jrperin/homeControl_esp8266/exemplos/server/server.ino

/*
The MIT License (MIT)
Copyright (c) 2015 Pedro Minatel
Permission is hereby granted, free of charge, to any person obtaining a copy
of this software and associated documentation files (the "Software"), to deal
in the Software without restriction, including without limitation the rights
to use, copy, modify, merge, publish, distribute, sublicense, and/or sell
copies of the Software, and to permit persons to whom the Software is
furnished to do so, subject to the following conditions:
The above copyright notice and this permission notice shall be included in all
copies or substantial portions of the Software.
THE SOFTWARE IS PROVIDED "AS IS", WITHOUT WARRANTY OF ANY KIND, EXPRESS OR
IMPLIED, INCLUDING BUT NOT LIMITED TO THE WARRANTIES OF MERCHANTABILITY,
FITNESS FOR A PARTICULAR PURPOSE AND NONINFRINGEMENT. IN NO EVENT SHALL THE
AUTHORS OR COPYRIGHT HOLDERS BE LIABLE FOR ANY CLAIM, DAMAGES OR OTHER
LIABILITY, WHETHER IN AN ACTION OF CONTRACT, TORT OR OTHERWISE, ARISING FROM,
OUT OF OR IN CONNECTION WITH THE SOFTWARE OR THE USE OR OTHER DEALINGS IN THE
SOFTWARE.
*/

#include <ESP8266WiFi.h>

const char* ssid = "ssid";
const char* password = "password";

WiFiServer server(80);

void setup() {
  Serial.begin(115200);
  delay(10);

  // prepare GPIO2
  pinMode(4, OUTPUT);
  digitalWrite(4, 0);

  pinMode(5, OUTPUT);
  digitalWrite(5, 0);
  
  // Connect to WiFi network
  Serial.println();
  Serial.println();
  Serial.print("Connecting to ");
  Serial.println(ssid);
  
  WiFi.begin(ssid, password);
  
  while (WiFi.status() != WL_CONNECTED) {
    delay(500);
    Serial.print(".");
  }
  
  Serial.println("");
  Serial.println("WiFi connected");
  
  // Start the server
  server.begin();
  Serial.println("Server started");
  Serial.println(WiFi.localIP());
}

void loop() {
  WiFiClient client = server.available();
  if (!client) {
    return;
  }
  
  Serial.println("new client");
  while(!client.available()){
    delay(1);
  }
  
  String req = client.readStringUntil('\r');
  Serial.println(req);
  client.flush();

  String buf = "";

  buf += "HTTP/1.1 200 OK\r\nContent-Type: text/html\r\n\r\n<!DOCTYPE HTML>\r\n<html>\r\n";
  buf += "<h3> ESP8266 Web Server</h3>";
  buf += "<p>GPIO4 <a href=\"?function=led4_on\"><button>ON</button></a> <a href=\"?function=led4_off\"><button>OFF</button></a></p>";
  buf += "<p>GPIO5 <a href=\"?function=led5_on\"><button>ON</button></a> <a href=\"?function=led5_off\"><button>OFF</button></a></p>";
  buf += "<h4>Criado por Pedro Minatel</h4>";
  buf += "</html>\n";

  client.print(buf);
  client.flush();
  
  if (req.indexOf("led5_on") != -1)
    digitalWrite(5, 1);
  else if (req.indexOf("led5_off") != -1)
    digitalWrite(5, 0);
  else if (req.indexOf("led4_on") != -1)
    digitalWrite(4, 1);
  else if (req.indexOf("led4_off") != -1)
    digitalWrite(4, 0);
  else {
    Serial.println("invalid request");
    client.stop();
  }
  Serial.println("Client disonnected");
}
